meltoner/NEM_UAVRC_MEGA/UAVRC_MEGA/Steer.h

/*
  Steer.h - Library for wraping the functions controling Steer
  Author - Konstantinos Papageorgiou kp at rei.gr 2022 
*/

#ifndef Steer_h
#define Steer_h

#include "Arduino.h"
#include <Servo.h>
#include "Context.h"

class Steer{
  public:
    Steer(byte pin);
    void setup(Context &_context);
    void apply();
    void setSteer(int value);
    int getHeadingDifference();

  private:
    byte _pin;
    boolean on = false;
    Servo steer;
    unsigned long applied = 0;
    Context *context;
};

#endif
