meltoner/NEM_UAVRC_MEGA/UAVRC_MEGA/Gps.h

/*
  Gps.h - Library for wraping the functions controling the Gpsnometer
  Author - Konstantinos Papageorgiou kp at rei.gr 2022
*/

#ifndef Gps_h
#define Gps_h

#include "Arduino.h" 
#include <TinyGPS++.h>
#include "Context.h"

class Gps{
  public:
    Gps(byte pin);
    void setup(Context &_context);
    void apply();
    void processTarget();
    void testStationary();

  private:
    Context *context;
    TinyGPSPlus gps;
};

#endif
