meltoner/NEM_UAVRC_MEGA/UAVRC_MEGA/Home.cpp

/*
  Home.h - Library for wraping the functions controling the Return to Home 
  Author - Konstantinos Papageorgiou kp at rei.gr 2022 
*/

#include "Arduino.h"
#include "Home.h" 
#include "Context.h" 

Home::Home(int pin){}

void Home::setup(Context &_context){
  context = &_context;
}

// Derive target heading and speed from gps target
void Home::apply(){
  
  // Update return to home gps target
  if( context->isSwitchC() && context->isGPSLocked ){    
    context->setGPSTarget( context->latlng[0], context->latlng[1]);
    context->targets[0] = context->targets[1];
  }

  context->toHomeActive = context->isSwitchD();
  
  if(context->toHomeActive){
    context->color = 5; // purple
    context->targets[0] = context->targets[1];

    for(int i = 0; i < 5; i++){
      if(context->targets[2] > distance[i]){
        context->toHomeSpeedWeight = speedWeight[i];
        if(context->toHomeWait){
          context->toHomeSpeedWeight = 0;
          context->intervals[7] = offTime[i];
        }else{
          context->intervals[7] = onTime[i];
        }
        break;
      }
    }
  }
}

void Home::bursts(){
  context->toHomeWait = !context->toHomeWait;
}
