meltoner/NEM_UAVRC_MEGA/UAVRC_MEGA/Remote.cpp

/*
  Remote.h - Library for wraping the functions Remote control i/o
  Author - Konstantinos Papageorgiou kp at rei.gr 2022
*/

#include "Arduino.h"
#include "Remote.h"
#include <IBusBM.h>

#define EXT_SENSORS 10

Remote::Remote(byte pin){}

void Remote::setup(Context &_context){
  context = &_context;
  IBusServo.begin(Serial2);
  delay(200); 
}

int Remote::readChannel(byte channelInput, int minLimit, int maxLimit, int defaultValue){ 
  uint16_t ch = IBusServo.readChannel(channelInput);
  if (ch < 100) 
    return defaultValue;
  return map(ch, 1000, 2000, minLimit, maxLimit);
}

void Remote::apply(){
  for(int i = 0; i < EXT_SENSORS; i++)
   context->ext_sensors[i] = (byte)readChannel(i, 0, 255, 0);
}
