meltoner/NEM_UAVRC_MEGA/UAVRC_MEGA/Mag.h

/*
  Mag.h - Library for wraping the functions controling the Magnometer
  Author - Konstantinos Papageorgiou kp at rei.gr 2022
*/
#ifndef Mag_h
#define Mag_h

#include "Arduino.h"
#include "Context.h"
#include <Adafruit_Sensor.h>
#include <Adafruit_HMC5883_U.h>

class Mag{
  public:
    Mag(byte pin);
    void setup(Context &_context);
    void apply();
    int pruneDegrees(float value);
    float getOffset();
    void initMagOffset();
    void updateMagOffset();
  private:
    Context *context;
    byte _pin;
    Adafruit_HMC5883_Unified mag;
    sensors_event_t event; 
};

#endif
