meltoner/NEM_UAVRC_MEGA/UAVRC_MEGA/Throttle.h

/*
  Throttle.h - Library for wraping the functions controling the Throttlenometer
  Author - Konstantinos Papageorgiou kp at rei.gr 2022 
*/
#ifndef Throttle_h
#define Throttle_h

#include "Arduino.h"
#include <Servo.h>
#include "Context.h"

class Throttle{
  public:
    Throttle(byte pin);
    void setup(Context &_context);
    void apply();
    void setThrottle(int value, int limiter);
  private:
    Context *context;
    Servo throttle;
    byte _pin;
};

#endif
